seonabrar/Smart-Watch/Smart_Watch_code/Logo.h

#include <sys/_intsup.h>
#ifndef _IMAGE_H_
#define _IMAGE_H_

extern const unsigned char gImage_heart[];
extern const unsigned char gImage_stepscount[];
extern const unsigned char gImage_temp[];
extern const unsigned char gImage_alt[];
extern const unsigned char gImage_time[];
#endif
